openenergymonitor/HeatpumpMonitor/HeatpumpMonitorTH/Hardware/v4/readme.md

# Heatpump monitor v4

## Schematic

[HeatpumpMonitor.brd](HeatpumpMonitor.brd)

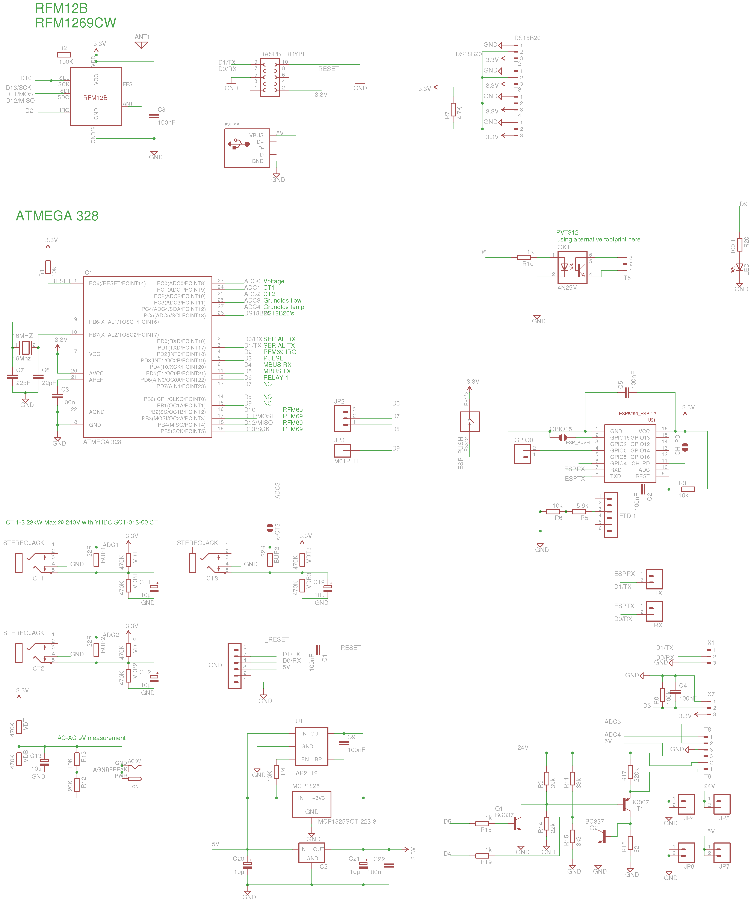
[picture p17: HeatpumpMonitorTH/Hardware/v4/schematic.png]


## Board

[HeatpumpMonitor.sch](HeatpumpMonitor.sch)

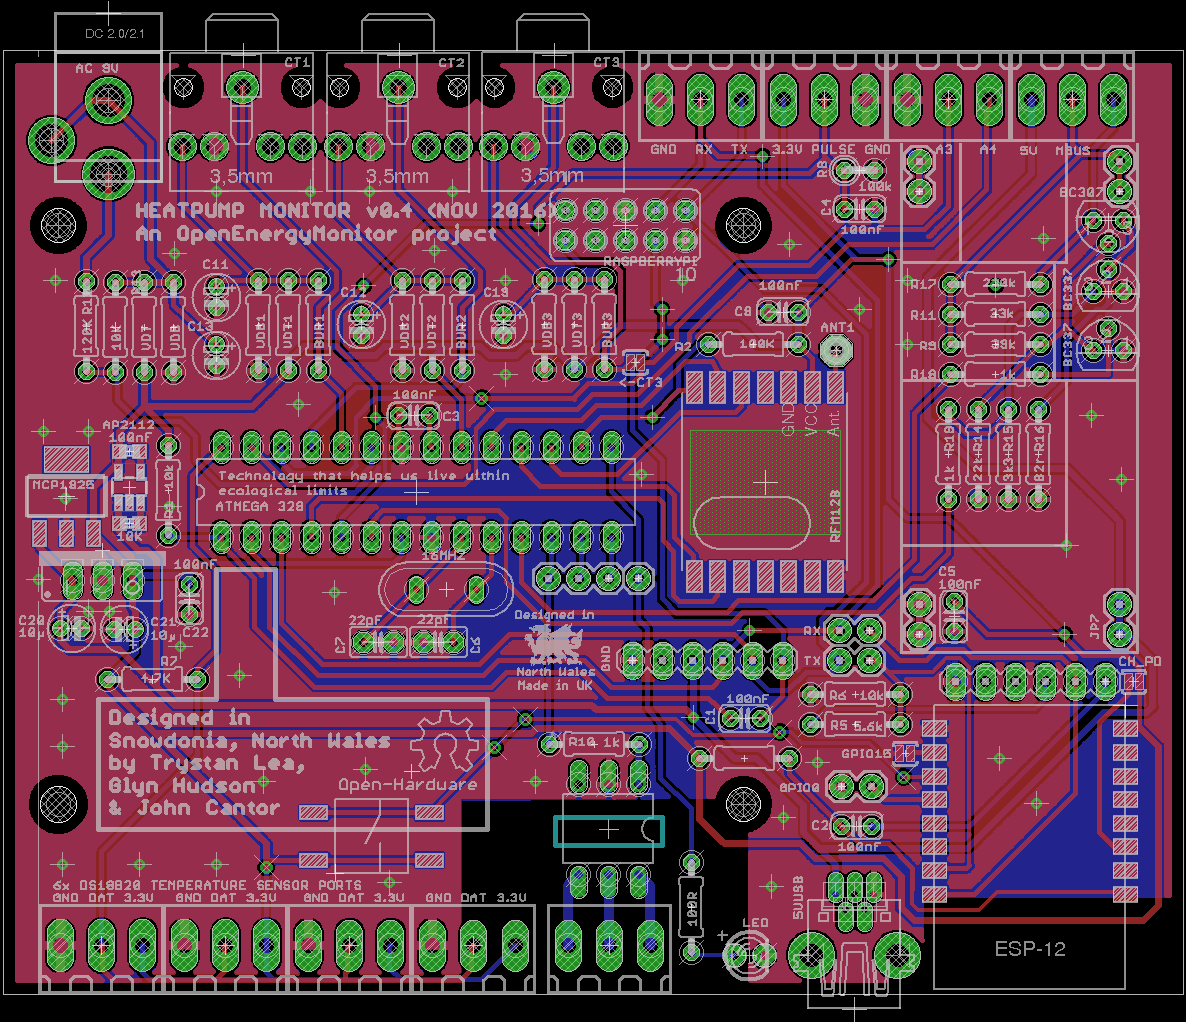
[picture p18: HeatpumpMonitorTH/Hardware/v4/board.png]


The hardware design (schematics, board files and gerber) files are licensed under the [Creative Commons Attribution-ShareAlike 3.0 Unported License](http://creativecommons.org/licenses/by-sa/3.0/) and follow the terms of the [OSHW (Open-source hardware) Statement of Principles 1.0.](http://freedomdefined.org/OSHW)
