openenergymonitor/HeatpumpMonitor/HeatpumpMonitorPi/baseboard/hpmon_pi_baseboard_brd.png

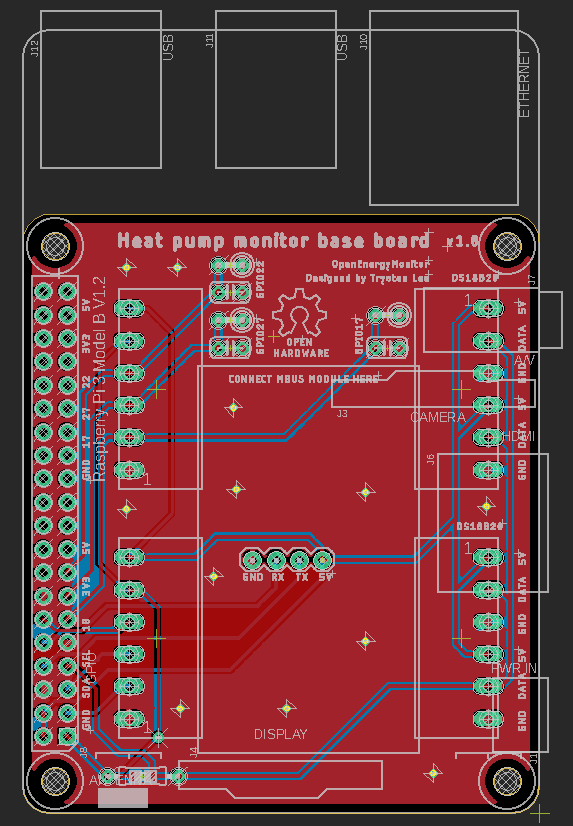
HeatpumpMonitorPi/baseboard/hpmon_pi_baseboard_brd.png
