openenergymonitor/HeatpumpMonitor/HeatpumpMonitorPi/baseboard/hpmon_pi_baseboard_sch.png

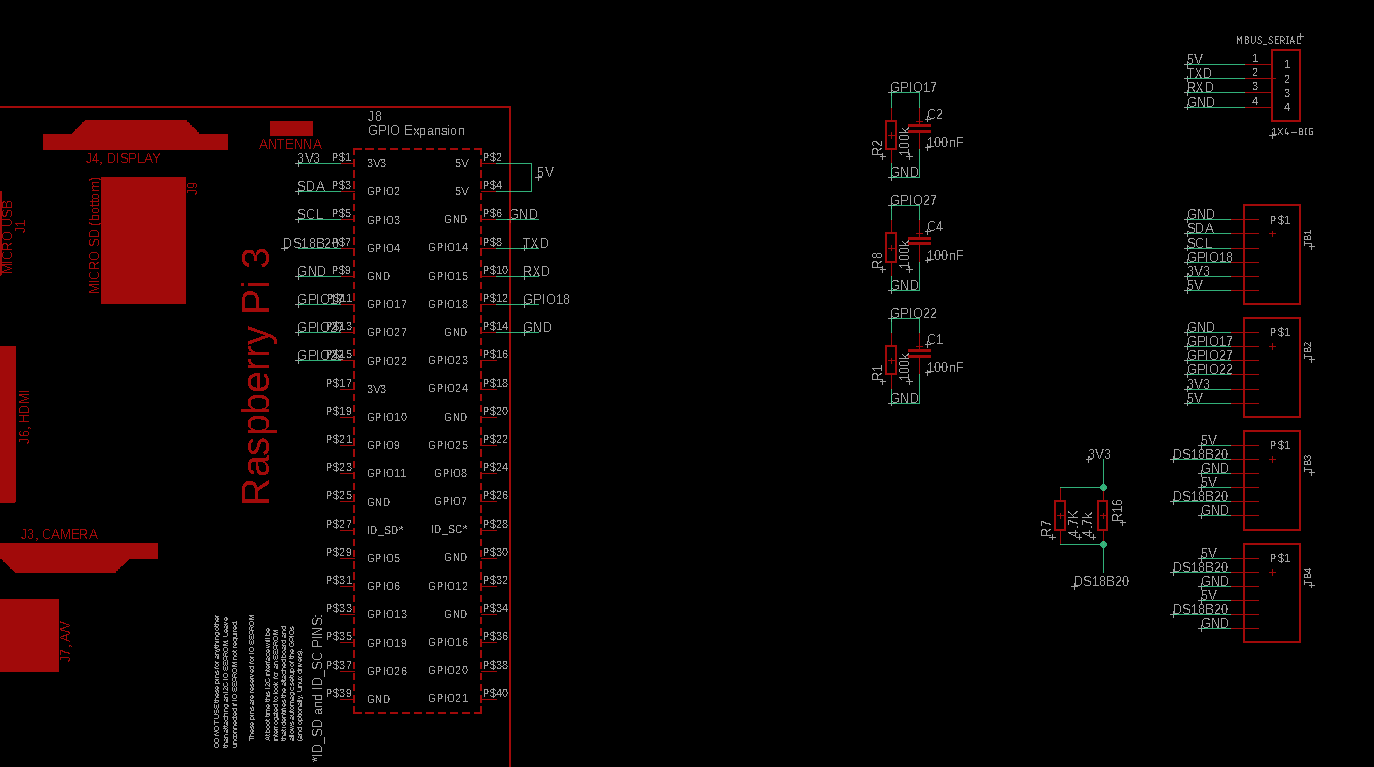
HeatpumpMonitorPi/baseboard/hpmon_pi_baseboard_sch.png
