openenergymonitor/HeatpumpMonitor/HeatpumpMonitorPi/images/heatpump_monitor_disconnected.jpg

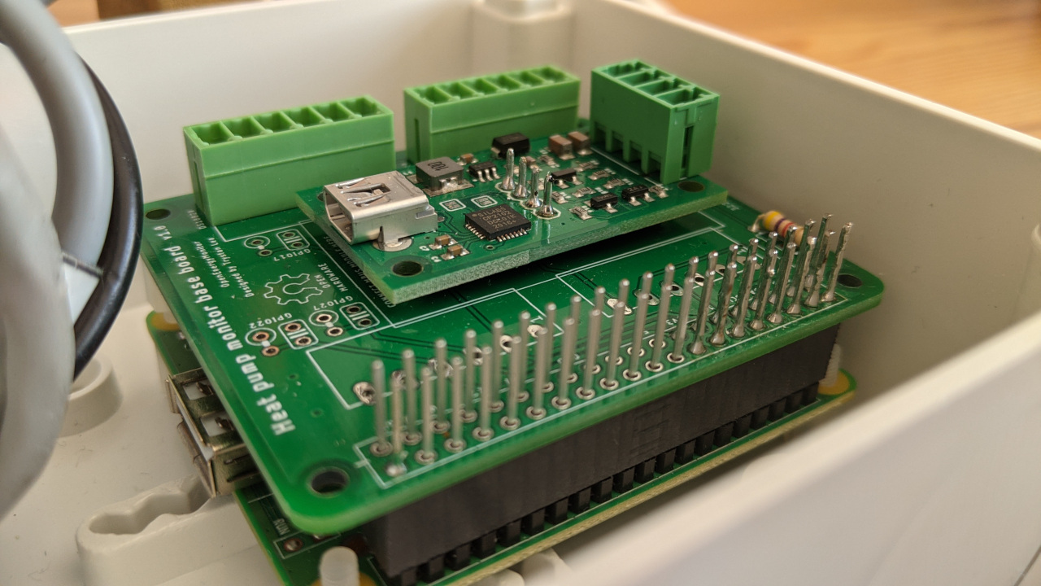
HeatpumpMonitorPi/images/heatpump_monitor_disconnected.jpg
