openenergymonitor/HeatpumpMonitor/HeatpumpMonitorPi/images/hpmon_small.jpg

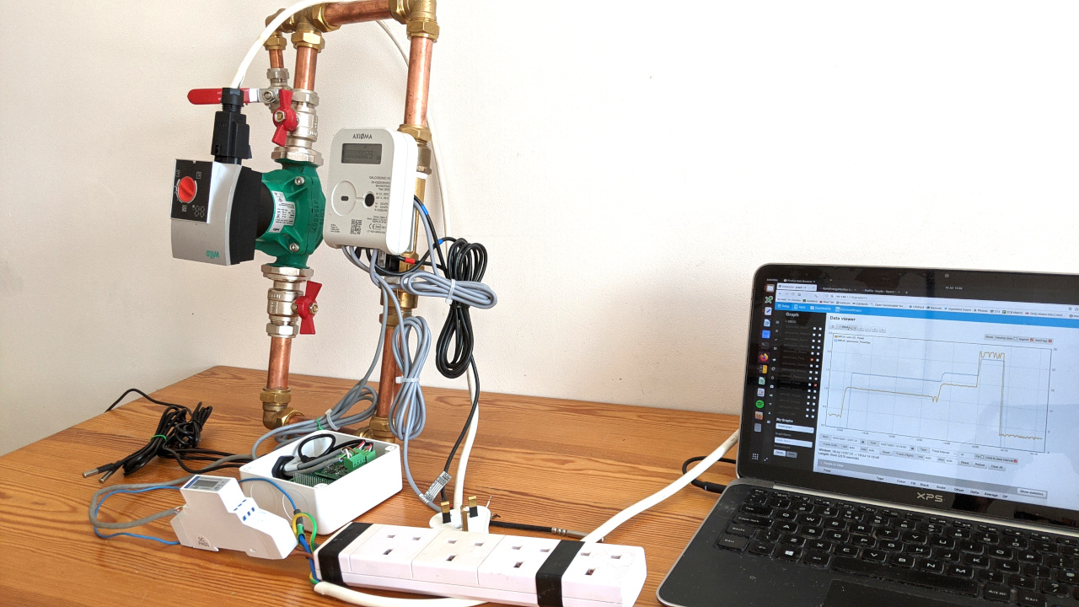
HeatpumpMonitorPi/images/hpmon_small.jpg
