openenergymonitor/HeatpumpMonitor/HeatpumpMonitorTH/images/board_view.jpg

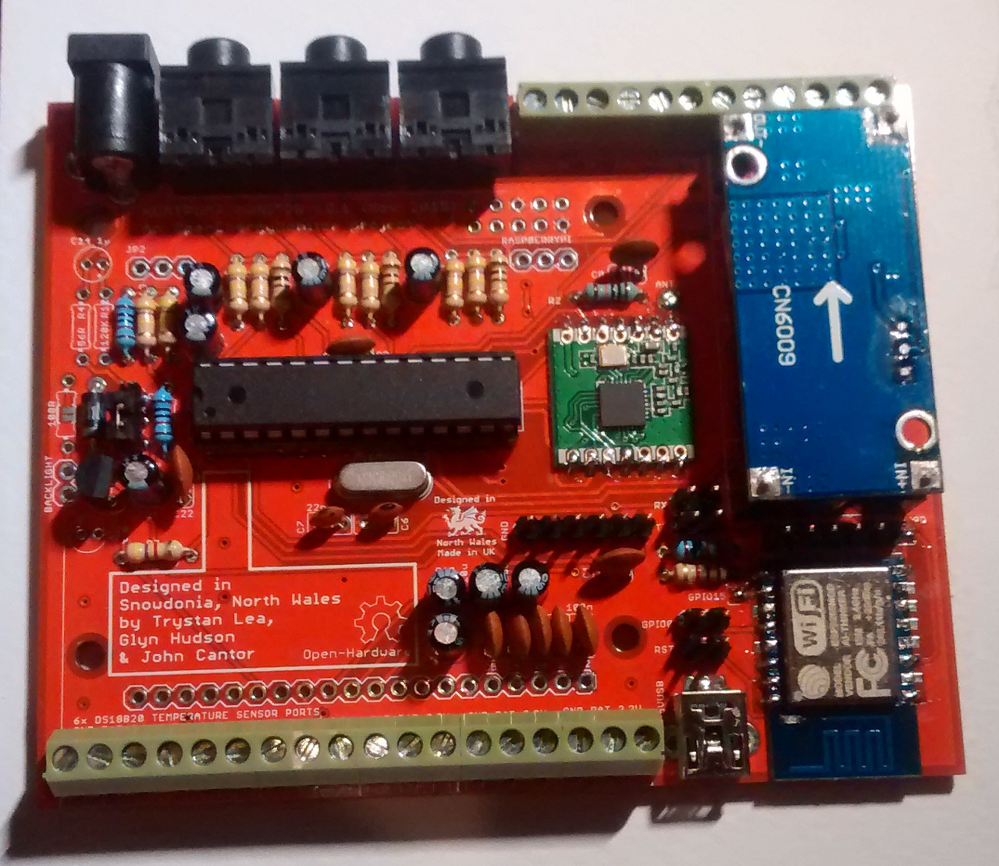
HeatpumpMonitorTH/images/board_view.jpg
