openenergymonitor/HeatpumpMonitor/HeatpumpMonitorTH/images/energymonitor_v2.JPG

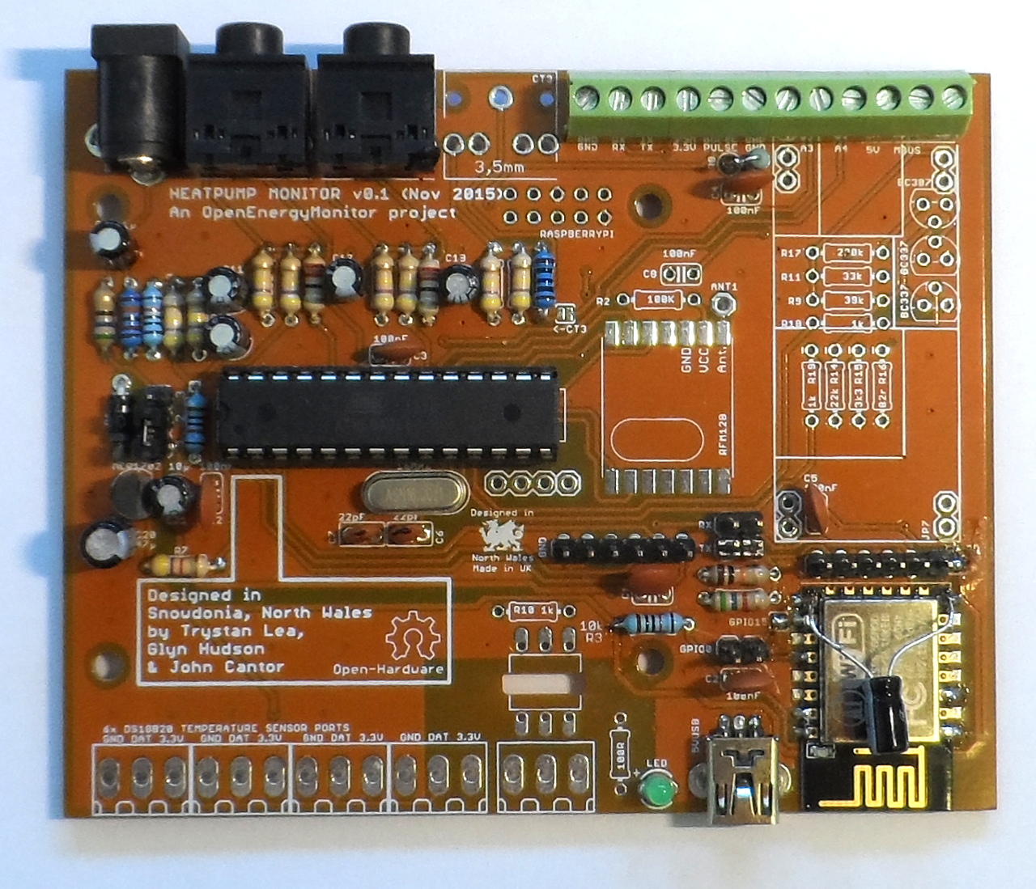
HeatpumpMonitorTH/images/energymonitor_v2.JPG
