openenergymonitor/HeatpumpMonitor/HeatpumpMonitorTH/images/heat-meter-pressure-drop-examples.JPG

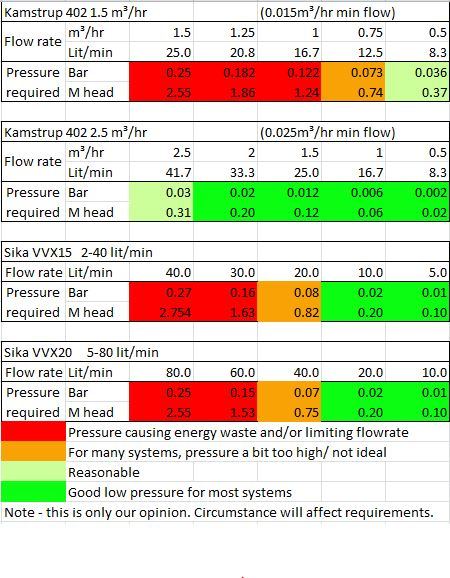
HeatpumpMonitorTH/images/heat-meter-pressure-drop-examples.JPG
