openenergymonitor/HeatpumpMonitor/HeatpumpMonitorTH/images/heatpump_monitor_v2.JPG

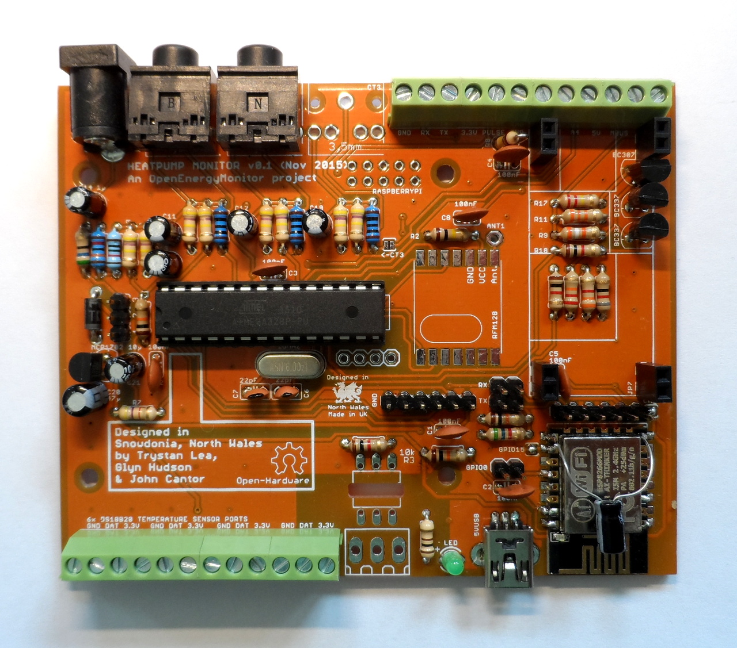
HeatpumpMonitorTH/images/heatpump_monitor_v2.JPG
