openenergymonitor/HeatpumpMonitor/HeatpumpMonitorTH/images/heatpump_monitor_v2b.JPG

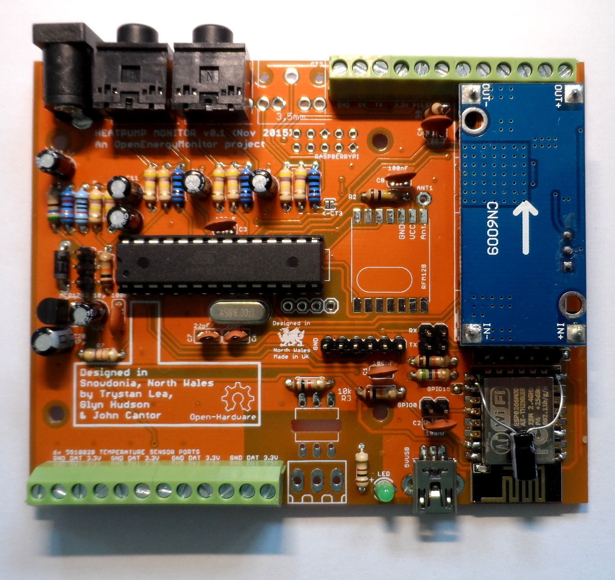
HeatpumpMonitorTH/images/heatpump_monitor_v2b.JPG
