openenergymonitor/HeatpumpMonitor/HeatpumpMonitorTH/images/pulseinput.jpg

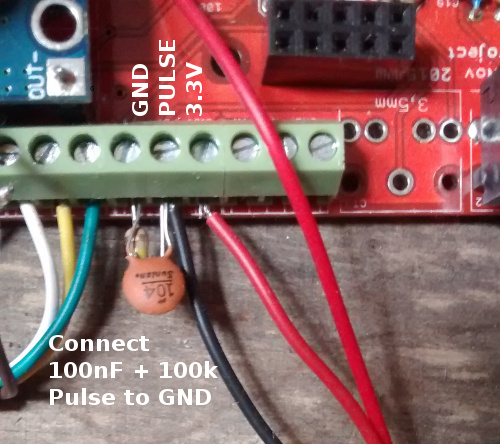
HeatpumpMonitorTH/images/pulseinput.jpg
