openenergymonitor/HeatpumpMonitor/HeatpumpMonitorTH/images/resistor-color-chart.jpg

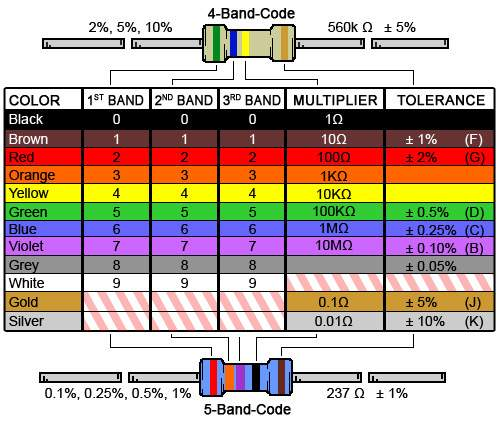
HeatpumpMonitorTH/images/resistor-color-chart.jpg
