openenergymonitor/HeatpumpMonitor/HeatpumpMonitorTH/images/terminal_connections.jpg

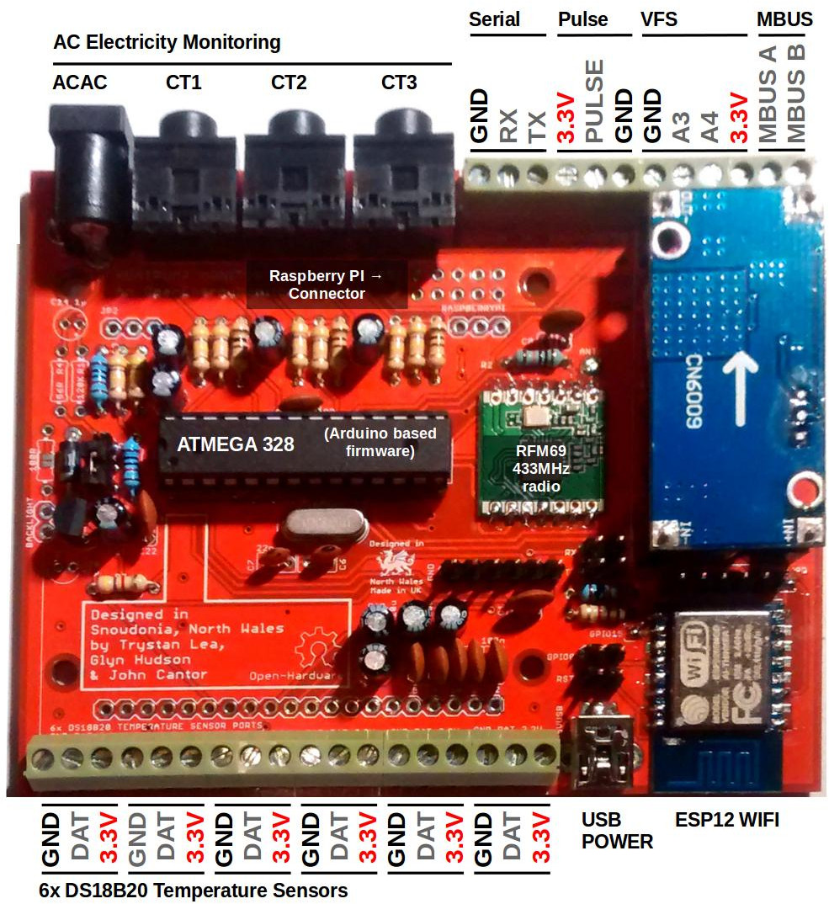
HeatpumpMonitorTH/images/terminal_connections.jpg
