openenergymonitor/HeatpumpMonitor/images/config/hpmon_config_emonpi_ct_mbus.png

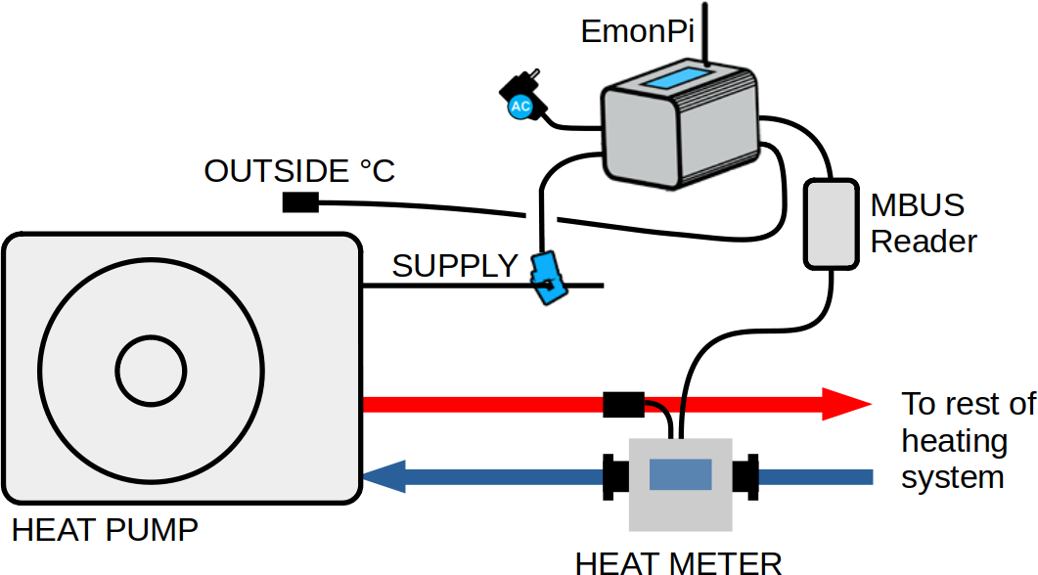
images/config/hpmon_config_emonpi_ct_mbus.png
