openenergymonitor/HeatpumpMonitor/images/config/hpmon_config_emonpi_ct_only.png

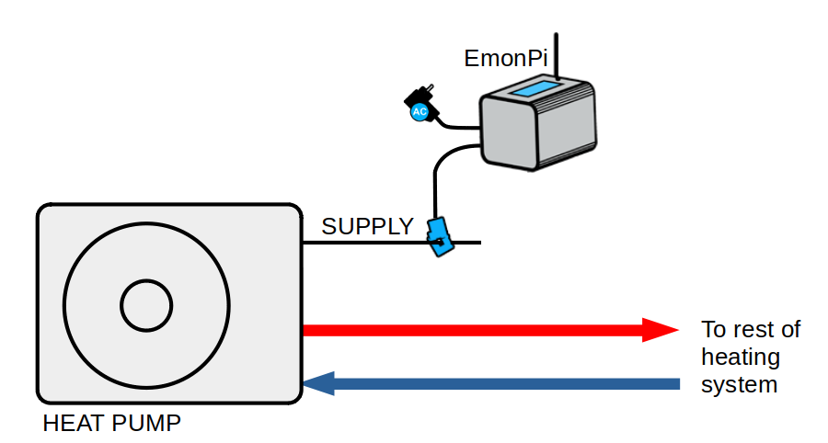
images/config/hpmon_config_emonpi_ct_only.png
