openenergymonitor/HeatpumpMonitor/images/config/hpmon_config_emontx_emonbase_ct_temps.png

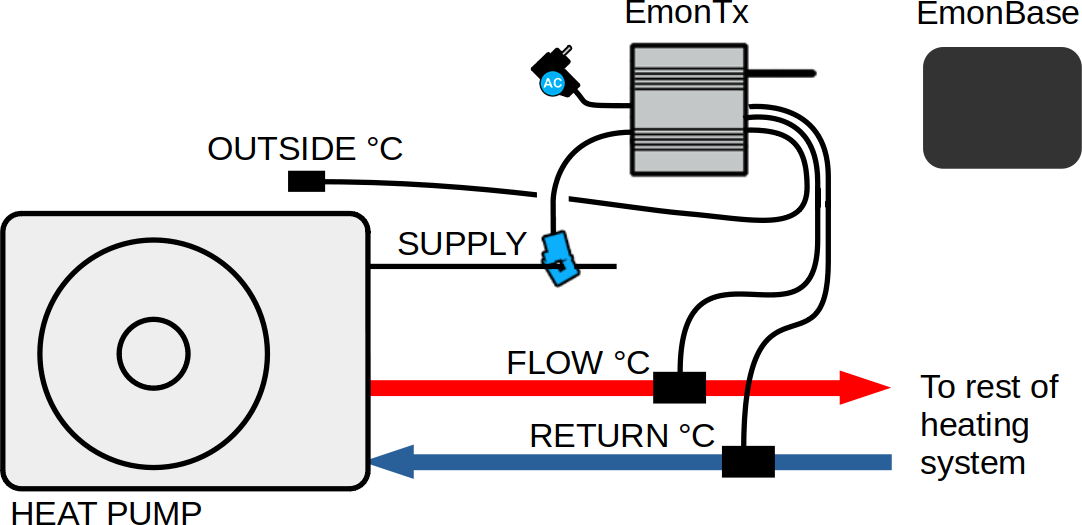
images/config/hpmon_config_emontx_emonbase_ct_temps.png
