openenergymonitor/HeatpumpMonitor/images/config/hpmon_config_emontx_wifi_ct_temps.png

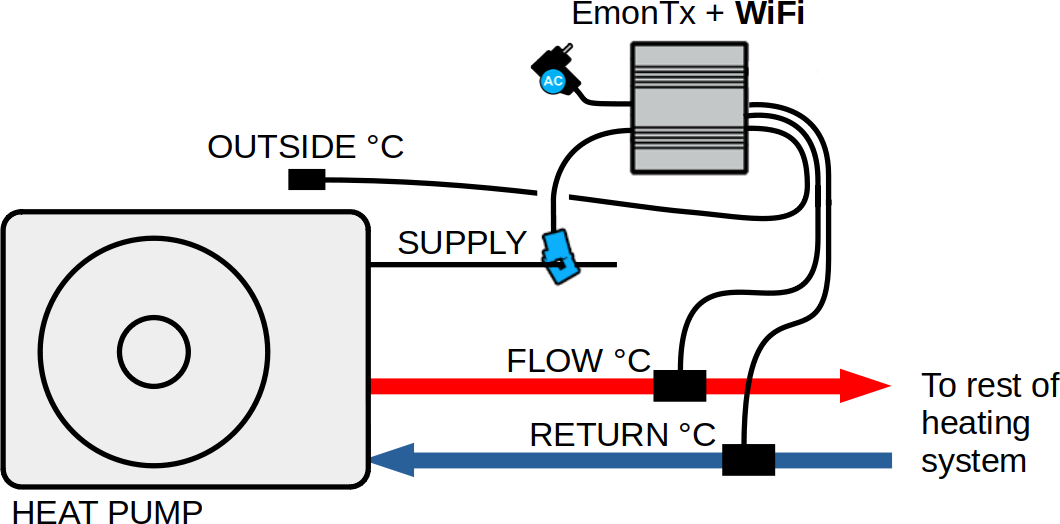
images/config/hpmon_config_emontx_wifi_ct_temps.png
