openenergymonitor/HeatpumpMonitor/images/config/hpmon_config_hpmonpi.png

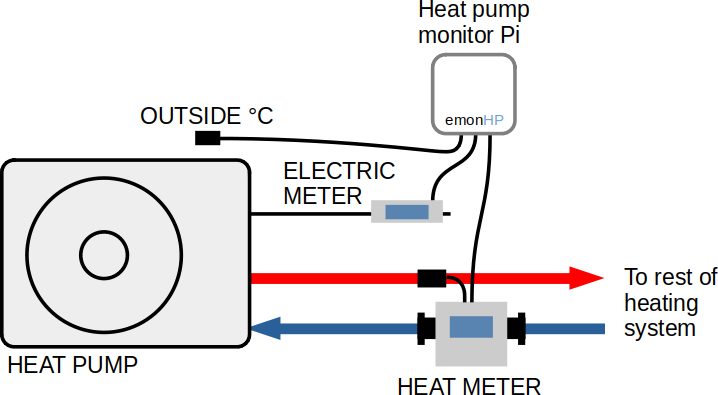
images/config/hpmon_config_hpmonpi.png
