openenergymonitor/HeatpumpMonitor/USB_MBUS_Reader/smt.png

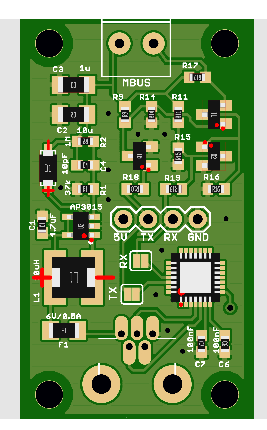
USB_MBUS_Reader/smt.png
