openenergymonitor/HeatpumpMonitor/WiFi_MBUS_Reader/v1_TH/v1_TH_mbus_uart.jpg

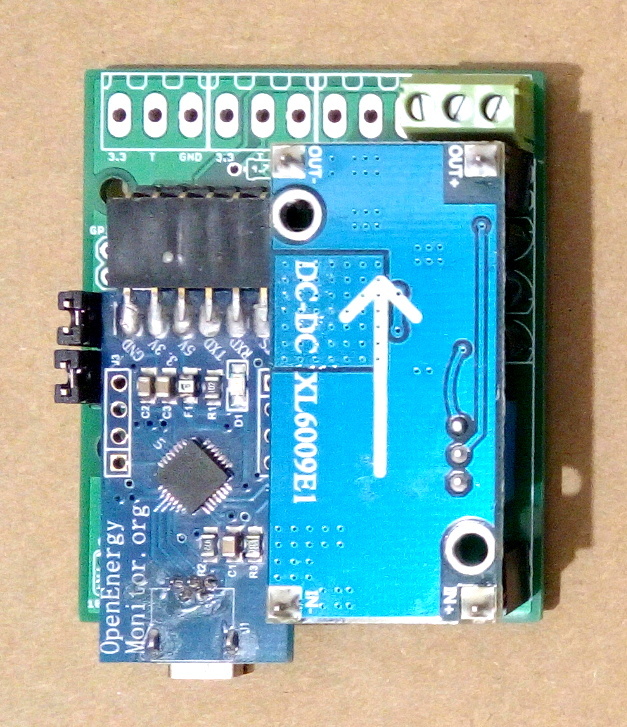
WiFi_MBUS_Reader/v1_TH/v1_TH_mbus_uart.jpg
