openenergymonitor/HeatpumpMonitor/HeatpumpMonitorTH/images/heatpump_monitor_v2_components.JPG

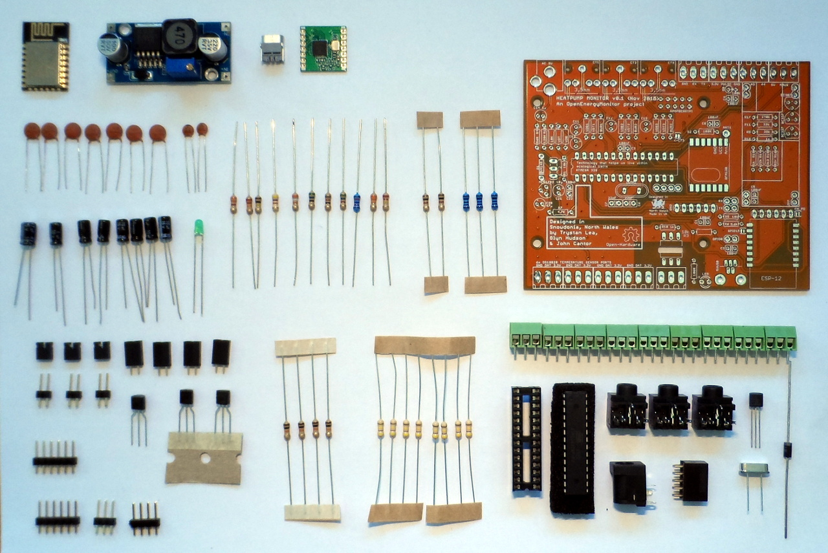
HeatpumpMonitorTH/images/heatpump_monitor_v2_components.JPG
